OpenSeizureDetector/ESP8266_SD/osd_app_orig/adxl345/adxl345.h

/*
 * ADXL345 FreeRTOS Library Header File
 * Based on the Arduino ADXL345 library at 
 *    https://github.com/jarzebski/Arduino-ADXL345
 * (c) 2014 Korneliusz Jarzebski (www.jarzebski.pl)
 * Copyright Graham Jones, 2017.
 * 
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
 */

#include "espressif/esp_common.h"
#include "../i2c/i2c.h"






#ifndef ADXL345_h
#define ADXL345_h

#define ADXL345_ADDRESS              (0x1D)
#define ADXL345_ALT_ADDRESS          (0x53)
#define ADXL345_DEVID                (0xe5)

// ADXL Register locations
#define ADXL345_REG_DEVID            (0x00)
#define ADXL345_REG_THRESH_TAP       (0x1D) // 1
#define ADXL345_REG_OFSX             (0x1E)
#define ADXL345_REG_OFSY             (0x1F)
#define ADXL345_REG_OFSZ             (0x20)
#define ADXL345_REG_DUR              (0x21) // 2
#define ADXL345_REG_LATENT           (0x22) // 3
#define ADXL345_REG_WINDOW           (0x23) // 4
#define ADXL345_REG_THRESH_ACT       (0x24) // 5
#define ADXL345_REG_THRESH_INACT     (0x25) // 6
#define ADXL345_REG_TIME_INACT       (0x26) // 7
#define ADXL345_REG_ACT_INACT_CTL    (0x27)
#define ADXL345_REG_THRESH_FF        (0x28) // 8
#define ADXL345_REG_TIME_FF          (0x29) // 9
#define ADXL345_REG_TAP_AXES         (0x2A)
#define ADXL345_REG_ACT_TAP_STATUS   (0x2B)
#define ADXL345_REG_BW_RATE          (0x2C)
#define ADXL345_REG_POWER_CTL        (0x2D)
#define ADXL345_REG_INT_ENABLE       (0x2E)
#define ADXL345_REG_INT_MAP          (0x2F)
#define ADXL345_REG_INT_SOURCE       (0x30) // A
#define ADXL345_REG_DATA_FORMAT      (0x31)
#define ADXL345_REG_DATAX0           (0x32)
#define ADXL345_REG_DATAX1           (0x33)
#define ADXL345_REG_DATAY0           (0x34)
#define ADXL345_REG_DATAY1           (0x35)
#define ADXL345_REG_DATAZ0           (0x36)
#define ADXL345_REG_DATAZ1           (0x37)
#define ADXL345_REG_FIFO_CTL         (0x38)
#define ADXL345_REG_FIFO_STATUS      (0x39)

#define ADXL345_GRAVITY_SUN          273.95f
#define ADXL345_GRAVITY_EARTH        9.80665f
#define ADXL345_GRAVITY_MOON         1.622f
#define ADXL345_GRAVITY_MARS         3.69f
#define ADXL345_GRAVITY_NONE         1.00f

#ifndef VECTOR_STRUCT_H
#define VECTOR_STRUCT_H
typedef struct 
{
  float XAxis;
  float YAxis;
  float ZAxis;
} ADXL345_Vector;
#endif

#ifndef IVECTOR_STRUCT_H
#define IVECTOR_STRUCT_H
typedef struct 
{
  int16_t XAxis;
  int16_t YAxis;
  int16_t ZAxis;
} ADXL345_IVector;
#endif

typedef enum
{
    ADXL345_DATARATE_3200HZ    = 0b1111,
    ADXL345_DATARATE_1600HZ    = 0b1110,
    ADXL345_DATARATE_800HZ     = 0b1101,
    ADXL345_DATARATE_400HZ     = 0b1100,
    ADXL345_DATARATE_200HZ     = 0b1011,
    ADXL345_DATARATE_100HZ     = 0b1010,
    ADXL345_DATARATE_50HZ      = 0b1001,
    ADXL345_DATARATE_25HZ      = 0b1000,
    ADXL345_DATARATE_12_5HZ    = 0b0111,
    ADXL345_DATARATE_6_25HZ    = 0b0110,
    ADXL345_DATARATE_3_13HZ    = 0b0101,
    ADXL345_DATARATE_1_56HZ    = 0b0100,
    ADXL345_DATARATE_0_78HZ    = 0b0011,
    ADXL345_DATARATE_0_39HZ    = 0b0010,
    ADXL345_DATARATE_0_20HZ    = 0b0001,
    ADXL345_DATARATE_0_10HZ    = 0b0000
} ADXL345_dataRate_t;

typedef enum
{
    ADXL345_INT2 = 0b01,
    ADXL345_INT1 = 0b00
} ADXL345_int_t;

typedef enum
{
    ADXL345_DATA_READY         = 0x07,
    ADXL345_SINGLE_TAP         = 0x06,
    ADXL345_DOUBLE_TAP         = 0x05,
    ADXL345_ACTIVITY           = 0x04,
    ADXL345_INACTIVITY         = 0x03,
    ADXL345_FREE_FALL          = 0x02,
    ADXL345_WATERMARK          = 0x01,
    ADXL345_OVERRUN            = 0x00
} ADXL345_activity_t;

typedef enum
{
    ADXL345_RANGE_16G          = 0b11,
    ADXL345_RANGE_8G           = 0b10,
    ADXL345_RANGE_4G           = 0b01,
    ADXL345_RANGE_2G           = 0b00
} ADXL345_range_t;


typedef struct
{
    bool isOverrun;
    bool isWatermark;
    bool isFreeFall;
    bool isInactivity;
    bool isActivity;
    bool isActivityOnX;
    bool isActivityOnY;
    bool isActivityOnZ;
    bool isDoubleTap;
    bool isTap;
    bool isTapOnX;
    bool isTapOnY;
    bool isTapOnZ;
    bool isDataReady;
} ADXL345_Activites;

//bool ADXL345_begin(void);
void ADXL345_clearSettings(void);

ADXL345_IVector ADXL345_readRaw(void);
ADXL345_Vector ADXL345_readNormalize(float gravityFactor);
ADXL345_Vector ADXL345_readScaled(void);

ADXL345_Activites ADXL345_readActivites(void);

ADXL345_Vector ADXL345_lowPassFilter(ADXL345_Vector vector, float alpha);

void  ADXL345_setRange(ADXL345_range_t range);
ADXL345_range_t ADXL345_getRange(void);

void  ADXL345_setDataRate(ADXL345_dataRate_t dataRate);
ADXL345_dataRate_t ADXL345_getDataRate(void);

void ADXL345_setTapThreshold(float threshold);
float ADXL345_getTapThreshold(void);

void ADXL345_setTapDuration(float duration);
float ADXL345_getTapDuration(void);

void ADXL345_setDoubleTapLatency(float latency);
float ADXL345_getDoubleTapLatency(void);

void ADXL345_setDoubleTapWindow(float window);
float ADXL345_getDoubleTapWindow(void);

void ADXL345_setActivityThreshold(float threshold);
float ADXL345_getActivityThreshold(void);

void ADXL345_setInactivityThreshold(float threshold);
float ADXL345_getInactivityThreshold(void);

void ADXL345_setTimeInactivity(uint8_t time);
uint8_t ADXL345_getTimeInactivity(void);

void ADXL345_setFreeFallThreshold(float threshold);
float ADXL345_getFreeFallThreshold(void);

void ADXL345_setFreeFallDuration(float duration);
float ADXL345_getFreeFallDuration();

void ADXL345_setActivityX(bool state);
bool ADXL345_getActivityX(void);
void ADXL345_setActivityY(bool state);
bool ADXL345_getActivityY(void);
void ADXL345_setActivityZ(bool state);
bool ADXL345_getActivityZ(void);
void ADXL345_setActivityXYZ(bool state);

void ADXL345_setInactivityX(bool state);
bool ADXL345_getInactivityX(void);
void ADXL345_setInactivityY(bool state);
bool ADXL345_getInactivityY(void);
void ADXL345_setInactivityZ(bool state);
bool ADXL345_getInactivityZ(void);
void ADXL345_setInactivityXYZ(bool state);

void ADXL345_setTapDetectionX(bool state);
bool ADXL345_getTapDetectionX(void);
void ADXL345_setTapDetectionY(bool state);
bool ADXL345_getTapDetectionY(void);
void ADXL345_setTapDetectionZ(bool state);
bool ADXL345_getTapDetectionZ(void);
void ADXL345_setTapDetectionXYZ(bool state);

void ADXL345_useInterrupt(ADXL345_int_t interrupt);

void ADXL345_enableFifo(void);
uint8_t ADXL345_getFifoStatus(void);
uint8_t ADXL345_getFifoCtl(void);
uint8_t ADXL345_setFifoCtl(uint8_t ctlVal);

uint8_t ADXL345_writeRegister8(uint8_t reg, uint8_t value);
uint8_t ADXL345_readRegister8(uint8_t reg);
uint8_t ADXL345_fastRegister8(uint8_t reg);
int16_t ADXL345_readRegister16(uint8_t reg);
void ADXL345_writeRegisterBit(uint8_t reg, uint8_t pos, bool state);
bool ADXL345_readRegisterBit(uint8_t reg, uint8_t pos);





// Function prototypes
uint8_t ADXL345_init(int scl, int sca);


#endif
