OpenSeizureDetector/ESP8266_SD/osd_esp/user/comms.c

/*
 * OpenSeizureDetector - ESP8266 Version.
 *
 * ESP8266_SD - a simple accelerometer based seizure detector that runs on 
 * an ESP8266 system on chip, with ADXL345 accelerometer attached by i2c 
 * interface.
 *
 * See http://openseizuredetector.org for more information.
 *
 * Copyright Graham Jones, 2015, 2016, 2017
 *
 * This file is part of ESP8266_SD.
 *
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
 * You should have received a copy of the GNU General Public License
 * along with ESP8266_SD.  If not, see <http://www.gnu.org/licenses/>.
 */

#include <string.h>

#include <freertos/FreeRTOS.h>
#include <freertos/task.h>

#include "lwip/err.h"
#include "lwip/sockets.h"
#include "lwip/sys.h"
#include "lwip/netdb.h"
#include "lwip/dns.h"

#include "spiffs.h"
#include "esp_spiffs.h"


#include "private_ssid_config.h"

#include "osd_app.h"


#define WEB_IPADDR "192.168.43.77"
#define WEB_PORT 8080
#define WEB_URL "http://chainxor.org/"

#define BUF_SIZE 2000
#define REQ_SIZE 200

/**
 * int sendHttpRequest(serverIp,url,serverPort,reqType,contType,data,
 *                            response,maxlen)
 * sends a http GET request to server *serverIp with *url, port serverPort 
 * Request type reqType is GET, POST etc.
 * Content type is application/json etc.
 * Character string data is included in the request body.
 * and put the response in *response
 * which should have maxLen bytes reserved for it.
 * returns the number of bytes read.
 */
int sendHttpRequest(char *serverIp, char *url, int serverPort, char *reqType,
		    char *contType, char *data,
		   char *response, int maxLen) {
  struct sockaddr_in ipaddr;
  static char req[REQ_SIZE];
  int ret;
  int s;  // socket id.
  
  if (debug) APP_LOG(APP_LOG_LEVEL_DEBUG,"sendHttpRequest(%s)", url);
  
  // set up server address
  memset(&ipaddr,0,sizeof(ipaddr));
  ipaddr.sin_len = sizeof(ipaddr);
  ipaddr.sin_family = AF_INET;
  ipaddr.sin_port = PP_HTONS(serverPort);
  ipaddr.sin_addr.s_addr = inet_addr(serverIp);
  printf("processed IP Address = %s\n", ipaddr_ntoa((ip_addr_t*)&(ipaddr.sin_addr.s_addr)));

  // create socket
  s = lwip_socket(AF_INET, SOCK_STREAM, 0);
  if(s < 0) {
    printf("sendHttpRequest()... Failed to allocate socket.");
    return -1;
  } else
      if (debug) APP_LOG(APP_LOG_LEVEL_DEBUG,
			 "sendHttpRequest() - allocated socket ok");

  // connect
  ret = lwip_connect(s, (struct sockaddr*)&ipaddr, sizeof(ipaddr));
  if(ret!=0) {
    close(s);
    printf("sendHttpRequest() - **** FAILED TO CONNECT ***\n");
    return -1 ;
  } else {
    if (debug) APP_LOG(APP_LOG_LEVEL_DEBUG,
		       "sendHttpRequest() - connected ok");
  }

  snprintf(req,REQ_SIZE,
    "%s %s HTTP/1.0\r\n"
    "User-Agent: esp-open-rtos/0.1 esp8266\r\n"
	   "Content-Type: %s\r\n"
	   "Content-Length:%d\r\n"
	   "\r\n"
	   "%s\r\n"
	   ,reqType,url,contType,strlen(data),data);
  if (debug) APP_LOG(APP_LOG_LEVEL_DEBUG,
		     "sendHttpRequest() - req=%s",req);
  if (lwip_write(s, req, strlen(req)) < 0) {
    printf("sendHttpRequest()... socket send failed");
  } else {
    if (debug) APP_LOG(APP_LOG_LEVEL_DEBUG,
		       "sendHttpRequest() - send ok");
  }

  // zero the response buffer, then read the response.
  bzero(response, maxLen);
  ret = lwip_read(s,response,maxLen);
  if (debug) APP_LOG(APP_LOG_LEVEL_DEBUG,
		     "sendHttpRequest() - Read data from socket - ret=%d.  response=%s.",ret,response);
  
  lwip_close(s);
  if (debug) APP_LOG(APP_LOG_LEVEL_DEBUG,
  		     "sendHttpRequest() - Socket closed - Returning %d",ret);
  return ret;
}

/** 
 * int sendGetRequest(serverIp,url,serverPort,response,maxlen)
 * sends a http GET request to server *serverIp with *url, port serverPort 
 * and put the response in *response
 * which should have maxLen bytes reserved for it.
 * returns the number of bytes read.
 */
int sendGetRequest(char *serverIp, char *url, int serverPort,
		   char *response, int maxLen) {
  int r;
  if (debug) APP_LOG(APP_LOG_LEVEL_DEBUG,"sendGetRequest(%s)", url);
  r = sendHttpRequest(serverIp,url,serverPort,
		      "GET","application/json","",response,maxLen);
  return r;
}

/** 
 * int sendPostRequest(serverIp,url,serverPort,data,response,maxlen)
 * sends a http GET request to server *serverIp with *url, port serverPort 
 * including *data in the header, and put the response in *response
 * which should have maxLen bytes reserved for it.
 * returns the number of bytes read.
 */
int sendPostRequest(char *serverIp, char *url, int serverPort, char *data,
		   char *response, int maxLen) {
  int r;
  if (debug) APP_LOG(APP_LOG_LEVEL_DEBUG,"sendPostRequest(%s)", url);
  r = sendHttpRequest(serverIp,url,serverPort,
		      "POST","application/json",data,response,maxLen);
  //if (debug) APP_LOG(APP_LOG_LEVEL_DEBUG,"sendPostRequest complete");
  return r;
}



/***************************************************
 * Send some Seizure Detector Data to the phone app.
 */

void sendSdData() {
  static char buf[BUF_SIZE];
  int ret;
  if (debug) APP_LOG(APP_LOG_LEVEL_DEBUG,"sendSdData()");
  ret = sendPostRequest(WEB_IPADDR,"/data",WEB_PORT,
			"{\"data\":{\"nsamp\":500,\"roiPower\":200,\"specPower\":30}}",
			buf,BUF_SIZE);
  if (debug) APP_LOG(APP_LOG_LEVEL_DEBUG,"sendSdData() - response=%d - %s",
		     ret,buf);

}
/*
  DictionaryIterator *iter;
  if (debug) APP_LOG(APP_LOG_LEVEL_DEBUG,"sendSdData()");
  app_message_outbox_begin(&iter);
  dict_write_uint8(iter,KEY_DATA_TYPE,(uint8_t)DATA_TYPE_RESULTS);
  dict_write_uint8(iter,KEY_ALARMSTATE,(uint8_t)alarmState);
  dict_write_uint32(iter,KEY_MAXVAL,(uint32_t)maxVal);
  dict_write_uint32(iter,KEY_MAXFREQ,(uint32_t)maxFreq);
  dict_write_uint32(iter,KEY_SPECPOWER,(uint32_t)specPower);
  dict_write_uint32(iter,KEY_ROIPOWER,(uint32_t)roiPower);
  dict_write_uint32(iter,KEY_ALARM_ROI,(uint32_t)alarmRoi);
  // Send simplified spectrum - just 10 integers so it fits in a message.
  dict_write_data(iter,KEY_SPEC_DATA,(uint8_t*)(&simpleSpec[0]),
		  10*sizeof(simpleSpec[0]));
  app_message_outbox_send();
  if (debug) APP_LOG(APP_LOG_LEVEL_DEBUG,"sent Results");
}
*/




/*************************************************************
 * Communications with Phone
 *************************************************************/
/*void inbox_received_callback(DictionaryIterator *iterator, void *context) {
  APP_LOG(APP_LOG_LEVEL_INFO, "Message received!");
  // Get the first pair
  Tuple *t = dict_read_first(iterator);

  int settingsChanged = 0;
  
  // Process all pairs present
  while(t != NULL) {
    // Process this pair's key
    APP_LOG(APP_LOG_LEVEL_INFO,"Key=%d",(int) t->key);
    switch (t->key) {
    case KEY_SETTINGS:
      APP_LOG(APP_LOG_LEVEL_INFO, "***********Phone Requesting Settings");
      sendSettings();
      break;
    case KEY_DATA_TYPE:
      APP_LOG(APP_LOG_LEVEL_INFO, "***********Phone Requesting Data");
      sendSdData();
      break;
    case KEY_SET_SETTINGS:
      APP_LOG(APP_LOG_LEVEL_INFO, "***********Phone Setting Settings");
      // We don't actually do anything here - the following sections
      // process the data and update the settings.
      break;
    case KEY_DEBUG:
      APP_LOG(APP_LOG_LEVEL_INFO,"Phone Setting DEBUG to %d",
	      debug = (int)t->value->int16);
      break;
    case KEY_DISPLAY_SPECTRUM:
      APP_LOG(APP_LOG_LEVEL_INFO,"Phone Setting DISPLAY_SPECTRUM to %d",
	      displaySpectrum = (int)t->value->int16);
      break;
    case KEY_SAMPLE_PERIOD:
      APP_LOG(APP_LOG_LEVEL_INFO,"Phone Setting SAMPLE_PERIOD to %d",
	      samplePeriod = (int)t->value->int16);
      settingsChanged = 1;
      break;
    case KEY_SAMPLE_FREQ:
      APP_LOG(APP_LOG_LEVEL_INFO,"Phone Setting SAMPLE_FREQ to %d",
	      sampleFreq = (int)t->value->int16);
      settingsChanged = 1;
      break;
    case KEY_FREQ_CUTOFF:
      APP_LOG(APP_LOG_LEVEL_INFO,"Phone Setting FREQ_CUTOFF to %d",
	      freqCutoff = (int)t->value->int16);
      settingsChanged = 1;
      break;
    case KEY_DATA_UPDATE_PERIOD:
      APP_LOG(APP_LOG_LEVEL_INFO,"Phone Setting DATA_UPDATE_PERIOD to %d",
	      dataUpdatePeriod = (int)t->value->int16);
      break;
    case KEY_SD_MODE:
      APP_LOG(APP_LOG_LEVEL_INFO,"Phone Setting SD_MODE to %d",
	      sdMode = (int)t->value->int16);
      break;
    case KEY_ALARM_FREQ_MIN:
      APP_LOG(APP_LOG_LEVEL_INFO,"Phone Setting ALARM_FREQ_MIN to %d",
	      alarmFreqMin = (int)t->value->int16);
      break;
    case KEY_ALARM_FREQ_MAX:
      APP_LOG(APP_LOG_LEVEL_INFO,"Phone Setting ALARM_FREQ_MAX to %d",
	      alarmFreqMax = (int)t->value->int16);
      break;
    case KEY_WARN_TIME:
      APP_LOG(APP_LOG_LEVEL_INFO,"Phone Setting WARN_TIME to %d",
	      warnTime = (int)t->value->int16);
      break;
    case KEY_ALARM_TIME:
      APP_LOG(APP_LOG_LEVEL_INFO,"Phone Setting ALARM_TIME to %d",
	      alarmTime = (int)t->value->int16);
      break;
    case KEY_ALARM_THRESH:
      APP_LOG(APP_LOG_LEVEL_INFO,"Phone Setting ALARM_THRESH to %d",
	      alarmThresh = (int)t->value->int16);
      break;
    case KEY_ALARM_RATIO_THRESH:
      APP_LOG(APP_LOG_LEVEL_INFO,"Phone Setting ALARM_RATIO_THRESH to %d",
	      alarmRatioThresh = (int)t->value->int16);
      break;
    case KEY_FALL_ACTIVE:
      APP_LOG(APP_LOG_LEVEL_INFO,"Phone Setting FALL_ACTIVE to %d",
	      fallActive = (int)t->value->int16);
      break;
    case KEY_FALL_THRESH_MIN:
      APP_LOG(APP_LOG_LEVEL_INFO,"Phone Setting FALL_THRESH_MIN to %d",
	      fallThreshMin = (int)t->value->int16);
      break;
    case KEY_FALL_THRESH_MAX:
      APP_LOG(APP_LOG_LEVEL_INFO,"Phone Setting FALL_THRESH_MAX to %d",
	      fallThreshMax = (int)t->value->int16);
      break;
    case KEY_FALL_WINDOW:
      APP_LOG(APP_LOG_LEVEL_INFO,"Phone Setting FALL_WINDOW to %d",
	      fallWindow = (int)t->value->int16);
      break;
    case KEY_MUTE_PERIOD:
      APP_LOG(APP_LOG_LEVEL_INFO,"Phone Setting MUTE_PERIOD to %d",
	      mutePeriod = (int)t->value->int16);
      break;
    case KEY_MAN_ALARM_PERIOD:
      APP_LOG(APP_LOG_LEVEL_INFO,"Phone Setting MAN_ALARM_PERIOD to %d",
	      manAlarmPeriod = (int)t->value->int16);
      break;
    }
    // Get next pair, if any
    t = dict_read_next(iterator);
  }
  if (settingsChanged) {
    APP_LOG(APP_LOG_LEVEL_DEBUG,"Accelerometer Settings Changed - resetting");
    analysis_init();
  }
}
*/

/*
void inbox_dropped_callback(AppMessageResult reason, void *context) {
  APP_LOG(APP_LOG_LEVEL_ERROR, "Message dropped!");
}
*/

/*
void outbox_failed_callback(DictionaryIterator *iterator, AppMessageResult reason, void *context) {
  APP_LOG(APP_LOG_LEVEL_ERROR, "Outbox send failed!");
}

void outbox_sent_callback(DictionaryIterator *iterator, void *context) {
  if (debug) APP_LOG(APP_LOG_LEVEL_INFO, "Outbox send success!");
}
*/

/*******************************************************
 * Send raw accelerometer data to the phone
 */
void sendRawData(ADXL345_IVector *data, uint32_t num_samples) {
  if (debug) APP_LOG(APP_LOG_LEVEL_DEBUG,"sendRawData() - num_samples=%d",num_samples);
}

/*void sendRawData(AccelData *data, uint32_t num_samples) {
  DictionaryIterator *iter;
  int32_t accData[25];  // 25 samples.
  for (uint8_t i=0;i<num_samples;i++) {
    accData[i] =
        data[i].x*data[i].x
      + data[i].y*data[i].y
      + data[i].z*data[i].z;
    //accData[3*i] = data[i].x;
    //accData[3*i+1] = data[i].y;
    //accData[3*i+2] = data[i].z;
  }
  if (debug) APP_LOG(APP_LOG_LEVEL_DEBUG,"sendRawData() - num_samples=%ld",num_samples);
  app_message_outbox_begin(&iter);
  dict_write_uint8(iter,KEY_DATA_TYPE,(uint8_t)DATA_TYPE_RAW);
  dict_write_uint32(iter,KEY_NUM_RAW_DATA,(uint32_t)num_samples);
  dict_write_data(iter,KEY_RAW_DATA,(uint8_t*)(accData),
		  num_samples*sizeof(accData[0]));
  app_message_outbox_send();
  if (debug) APP_LOG(APP_LOG_LEVEL_DEBUG,"sent Results");
}
*/

/***************************************************
 * Send Seizure Detector Settings to the Phone
 */
/*
void sendSettings() {
  DictionaryIterator *iter;
  APP_LOG(APP_LOG_LEVEL_INFO, "sendSettings()");
  app_message_outbox_begin(&iter);
  // Tell the phone this is settings data
  dict_write_uint8(iter,KEY_DATA_TYPE,(uint8_t)DATA_TYPE_SETTINGS);
  dict_write_uint8(iter,KEY_SETTINGS,(uint8_t)1);
  // then the actual settings
  dict_write_uint32(iter,KEY_DEBUG,(uint32_t)debug);
  dict_write_uint32(iter,KEY_DISPLAY_SPECTRUM,(uint32_t)displaySpectrum);
  // first the app version number
  dict_write_uint8(iter,KEY_VERSION_MAJOR,
		   (uint8_t)__pbl_app_info.process_version.major);
  dict_write_uint8(iter,KEY_VERSION_MINOR,
		   (uint8_t)__pbl_app_info.process_version.minor);
  // then the settings
  dict_write_uint32(iter,KEY_SAMPLE_PERIOD,(uint32_t)samplePeriod);
  dict_write_uint32(iter,KEY_SAMPLE_FREQ,(uint32_t)sampleFreq);
  dict_write_uint32(iter,KEY_FREQ_CUTOFF,(uint32_t)freqCutoff);
  dict_write_uint32(iter,KEY_DATA_UPDATE_PERIOD,(uint32_t)dataUpdatePeriod);
  dict_write_uint32(iter,KEY_SD_MODE,(uint32_t)sdMode);
  dict_write_uint32(iter,KEY_ALARM_FREQ_MIN,(uint32_t)alarmFreqMin);
  dict_write_uint32(iter,KEY_ALARM_FREQ_MAX,(uint32_t)alarmFreqMax);
  dict_write_uint32(iter,KEY_NMIN,(uint32_t)nMin);
  dict_write_uint32(iter,KEY_NMAX,(uint32_t)nMax);
  dict_write_uint32(iter,KEY_WARN_TIME,(uint32_t)warnTime);
  dict_write_uint32(iter,KEY_ALARM_TIME,(uint32_t)alarmTime);
  dict_write_uint32(iter,KEY_ALARM_THRESH,(uint32_t)alarmThresh);
  dict_write_uint32(iter,KEY_ALARM_RATIO_THRESH,(uint32_t)alarmRatioThresh);
  BatteryChargeState charge_state = battery_state_service_peek();
  dict_write_uint8(iter,KEY_BATTERY_PC,(uint8_t)charge_state.charge_percent);
  dict_write_uint32(iter,KEY_FALL_ACTIVE,(uint32_t)fallActive);
  dict_write_uint32(iter,KEY_FALL_THRESH_MIN,(uint32_t)fallThreshMin);
  dict_write_uint32(iter,KEY_FALL_THRESH_MAX,(uint32_t)fallThreshMax);
  dict_write_uint32(iter,KEY_FALL_WINDOW,(uint32_t)fallWindow);
  dict_write_uint32(iter,KEY_MUTE_PERIOD,(uint32_t)mutePeriod);
  dict_write_uint32(iter,KEY_MAN_ALARM_PERIOD,(uint32_t)manAlarmPeriod);

  app_message_outbox_send();

}
*/

void comms_init() {
  APP_LOG(APP_LOG_LEVEL_INFO, "comms_init()");

  struct station_config config = {
    .ssid = WIFI_SSID,
    .password = WIFI_PASS,
  };
  
  /* required to call wifi_set_opmode before station_set_config */
  wifi_set_opmode(STATION_MODE);
  wifi_station_set_config(&config);
  wifi_station_connect();

  
  /*
  // Register comms callbacks
  app_message_register_inbox_received(inbox_received_callback);
  APP_LOG(APP_LOG_LEVEL_INFO, "comms_init() - registered inbox_received_callback.");
  app_message_register_inbox_dropped(inbox_dropped_callback);
  APP_LOG(APP_LOG_LEVEL_INFO, "comms_init() - registered inbox_dropped_callback.");
  app_message_register_outbox_failed(outbox_failed_callback);
  APP_LOG(APP_LOG_LEVEL_INFO, "comms_init() - registered outbox_failed_callback.");
  app_message_register_outbox_sent(outbox_sent_callback);
  APP_LOG(APP_LOG_LEVEL_INFO, "comms_init() - registered outbox_failed_callback.");
  // Open AppMessage
  //int retVal = app_message_open(app_message_inbox_size_maximum(), 
  //		   app_message_outbox_size_maximum());
  int retVal = app_message_open(INBOX_SIZE, 
  				OUTBOX_SIZE);

  if (retVal == APP_MSG_OK) 
    APP_LOG(APP_LOG_LEVEL_INFO, "comms_init() - app_message_open() Success - retVal=%d, inbox_size=%d, outbox_size=%d",retVal,
	  INBOX_SIZE,
	  OUTBOX_SIZE);
  else if (retVal == APP_MSG_OUT_OF_MEMORY)
    APP_LOG(APP_LOG_LEVEL_ERROR, "comms_init() - app_message_open() **** OUT_OF_MEMORY **** - retVal=%d, max_inbox_size=%d, max_outbox_size=%d",retVal,
	  INBOX_SIZE,
	  OUTBOX_SIZE);
  else
    APP_LOG(APP_LOG_LEVEL_ERROR, "comms_init() - app_message_open() - retVal=%d, max_inbox_size=%d, max_outbox_size=%d",retVal,
	  INBOX_SIZE,
	  OUTBOX_SIZE);

  */


}


/* 
 *  waits for a message from the queue.  When received, sends
 *  the SD Data to the server.
*/
void commsTask(void *pvParameters)
{
  xQueueHandle *commsQueue = (xQueueHandle *)pvParameters;

  while(1) {
    uint32_t data_ts;
    xQueueReceive(*commsQueue, &data_ts, portMAX_DELAY);
    APP_LOG(APP_LOG_LEVEL_INFO, "commsTask()");
    sendSdData();
  }
}
