OpenSeizureDetector/ESP8266_SD/osd_esp/driver/i2c.c

/* 
 * The MIT License (MIT)
 * 
 * Copyright (c) 2015 Johan Kanflo (github.com/kanflo)
 *               2017 Graham Jones (github.com/jones139)
 * 
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
 * THE SOFTWARE IS PROVIDED "AS IS", WITHOUT WARRANTY OF ANY KIND, EXPRESS OR
 * IMPLIED, INCLUDING BUT NOT LIMITED TO THE WARRANTIES OF MERCHANTABILITY,
 * FITNESS FOR A PARTICULAR PURPOSE AND NONINFRINGEMENT. IN NO EVENT SHALL THE
 * AUTHORS OR COPYRIGHT HOLDERS BE LIABLE FOR ANY CLAIM, DAMAGES OR OTHER
 * LIABILITY, WHETHER IN AN ACTION OF CONTRACT, TORT OR OTHERWISE, ARISING FROM,
 * OUT OF OR IN CONNECTION WITH THE SOFTWARE OR THE USE OR OTHER DEALINGS IN
 * THE SOFTWARE.
 */

/**
 * Note:  This is the esp-open-rtos sdk i2c driver modified to work with the
 *        Espressif RTOS sdk rather than esp-open-rtos.
 *        I did this because esp-open-rtos does not support low power sleep
 *        functions which I need, and it looks too hard to reverse engineer
 *        it.
 *        Graham Jones, August 2017.
 */

#include <espressif/esp_common.h>
#include <espressif/esp8266/esp8266.h>
//#include <espressif/esp_misc.h> // sdk_os_delay_us
//#include <espressif/esp_system.h>
#include "i2c.h"
#include "gpio.h"

#define I2C_DEBUG true

#ifdef I2C_DEBUG
#define debug(fmt, ...) printf("%s: " fmt "\n", "I2C", ## __VA_ARGS__)
#else
#define debug(fmt, ...)
#endif

#define CLK_STRETCH  (10)

static bool started;
static bool flag;
static bool force;
static uint8_t freq ;
static uint8_t g_scl_pin;
static uint8_t g_sda_pin;

//Return the Multiplexer value associated with gpio Pin number gpioPin
int gpioPin2Mux(int gpioPin) {
  switch (gpioPin) {
  case 0:
    return GPIO_PIN_REG_0;
  case 1:
    return GPIO_PIN_REG_1;
  case 2:
    return GPIO_PIN_REG_2;
  case 3:
    return GPIO_PIN_REG_3;
  case 4:
    return GPIO_PIN_REG_4;
  case 5:
    return GPIO_PIN_REG_5;
  case 6:
    return GPIO_PIN_REG_6;
  case 7:
    return GPIO_PIN_REG_7;
  case 8:
    return GPIO_PIN_REG_8;
  case 9:
    return GPIO_PIN_REG_9;
  case 10:
    return GPIO_PIN_REG_10;
  case 11:
    return GPIO_PIN_REG_11;
  case 12:
    return GPIO_PIN_REG_12;
  case 13:
    return GPIO_PIN_REG_13;
  case 14:
    return GPIO_PIN_REG_14;
  case 15:
    return GPIO_PIN_REG_15;
  default:
    return -1;
  }
  
}

//Return the gpio func value associated with gpio Pin number gpioPin
int gpioPin2Func(int gpioPin) {
  switch (gpioPin) {
    case 0:
      return FUNC_GPIO0;
    case 1:
      return FUNC_GPIO1;
    case 2:
      return FUNC_GPIO2;
    case 3:
      return FUNC_GPIO3;
    case 4:
      return FUNC_GPIO4;
    case 5:
      return FUNC_GPIO5;
    case 6:
      return FUNC_GPIO6;
    case 7:
      return FUNC_GPIO7;
    case 8:
      return FUNC_GPIO8;
    case 9:
      return FUNC_GPIO9;
    case 10:
      return FUNC_GPIO10;
    default:
      return -1;
    }
}

#define I2C_GPIO_SET(pin)  \
    gpio_output_set(1<<pin,0,1<<pin,0)

#define I2C_GPIO_CLR(pin) \
    gpio_output_set(0,1<<pin,1<<pin,0)

#define gpio_write(pin,val) \
    if(val) I2C_GPIO_SET(pin);\
    else I2C_GPIO_CLR(pin)

// return value of GPIO pin pin.
uint8 gpio_read(int pin) {
  uint8 val; 
  ETS_INTR_LOCK(); 
  val = GPIO_INPUT_GET(GPIO_ID_PIN(pin));
  ETS_INTR_UNLOCK(); 
  return val;
}

inline bool i2c_status(void)
{
    return started;
}

void i2c_init(uint8_t scl_pin, uint8_t sda_pin)
{
  printf("i2c_init - GJ Version\n");
    started = false;
    flag = false ;
    g_scl_pin = scl_pin;
    g_sda_pin = sda_pin;

    int sda_mux, scl_mux;
    int sda_func, scl_func;

    PIN_FUNC_SELECT(gpioPin2Mux(g_sda_pin), gpioPin2Func(g_sda_pin));
    PIN_FUNC_SELECT(gpioPin2Mux(g_scl_pin), gpioPin2Func(g_scl_pin));

    GPIO_REG_WRITE(
		   GPIO_PIN_ADDR(GPIO_ID_PIN(g_sda_pin)),
		   GPIO_REG_READ(GPIO_PIN_ADDR(GPIO_ID_PIN(g_sda_pin)))
		   | GPIO_PIN_PAD_DRIVER_SET(GPIO_PAD_DRIVER_ENABLE)
		   ); //open drain
    GPIO_REG_WRITE(
		   GPIO_ENABLE_ADDRESS,
		   GPIO_REG_READ(GPIO_ENABLE_ADDRESS) | (1 << g_sda_pin)
		   );
    GPIO_REG_WRITE(GPIO_PIN_ADDR(GPIO_ID_PIN(g_scl_pin)),
		   GPIO_REG_READ(GPIO_PIN_ADDR(GPIO_ID_PIN(g_scl_pin)))
		   | GPIO_PIN_PAD_DRIVER_SET(GPIO_PAD_DRIVER_ENABLE)
		   ); //open drain;
    GPIO_REG_WRITE(GPIO_ENABLE_ADDRESS,
		   GPIO_REG_READ(GPIO_ENABLE_ADDRESS) | (1 << g_scl_pin)
		   );

    // I2C bus idle state.
    gpio_write(g_scl_pin, 1);
    gpio_write(g_sda_pin, 1);

    ETS_GPIO_INTR_ENABLE() ;

    // Prevent user, if frequency is high
    //if (system_get_cpu_freq() == SYS_CPU_80MHZ)
    //    if (I2C_CUSTOM_DELAY_80MHZ == 1)
    //        debug("Max frequency is 320Khz at 80MHz");
}

static inline void i2c_delay(void)
{
    uint32_t delay;
    if (freq == SYS_CPU_160MHZ)
    {
        __asm volatile (
            "movi %0, %1" "\n"
            "1: addi %0, %0, -1" "\n"
            "bnez %0, 1b" "\n"
        : "=a" (delay) : "i" (I2C_CUSTOM_DELAY_160MHZ));
    }
    else
    {
        __asm volatile (
            "movi %0, %1" "\n"
            "1: addi %0, %0, -1" "\n"
            "bnez %0, 1b" "\n"
        : "=a" (delay) : "i" (I2C_CUSTOM_DELAY_80MHZ));
    }
}

// Set SCL as input, allowing it to float high, and return current
// level of line, 0 or 1
static inline bool read_scl(void)
{
    gpio_write(g_scl_pin, 1);
    return gpio_read(g_scl_pin); // Clock high, valid ACK
}

// Set SDA as input, allowing it to float high, and return current
// level of line, 0 or 1
static inline bool read_sda(void)
{
    gpio_write(g_sda_pin, 1);
    // TODO: Without this delay we get arbitration lost in i2c_stop
    i2c_delay();
    return gpio_read(g_sda_pin); // Clock high, valid ACK
}

// Actively drive SCL signal low
static inline void clear_scl(void)
{
    gpio_write(g_scl_pin, 0);
}

// Actively drive SDA signal low
static inline void clear_sda(void)
{
    gpio_write(g_sda_pin, 0);
}

// Output start condition
void i2c_start(void)
{
    uint32_t clk_stretch = CLK_STRETCH;
    freq = system_get_cpu_freq();
    if (started) { // if started, do a restart cond
        // Set SDA to 1
        (void) read_sda();
        i2c_delay();
        while (read_scl() == 0 && clk_stretch--) ;
        // Repeated start setup time, minimum 4.7us
        i2c_delay();
    }
    started = true;
    if (read_sda() == 0) {
        debug("arbitration lost in i2c_start");
    }
    // SCL is high, set SDA from 1 to 0.
    clear_sda();
    i2c_delay();
    clear_scl();
}

// Output stop condition
bool i2c_stop(void)
{
    uint32_t clk_stretch = CLK_STRETCH;
    // Set SDA to 0
    clear_sda();
    i2c_delay();
    // Clock stretching
    while (read_scl() == 0 && clk_stretch--) ;
    // Stop bit setup time, minimum 4us
    i2c_delay();
    // SCL is high, set SDA from 0 to 1
    if (read_sda() == 0) {
        debug("arbitration lost in i2c_stop");
    }
    i2c_delay();
    if (!started) {
        debug("link was break!");
        return false ; //If bus was stop in other way, the current transmission Failed
    }
    started = false;
    return true;
}

// Write a bit to I2C bus
static void i2c_write_bit(bool bit)
{
    uint32_t clk_stretch = CLK_STRETCH;
    if (bit) {
        (void) read_sda();
    } else {
        clear_sda();
    }
    i2c_delay();
    // Clock stretching
    while (read_scl() == 0 && clk_stretch--) ;
    // SCL is high, now data is valid
    // If SDA is high, check that nobody else is driving SDA
    if (bit && read_sda() == 0) {
        debug("arbitration lost in i2c_write_bit");
    }
    i2c_delay();
    clear_scl();
}

// Read a bit from I2C bus
static bool i2c_read_bit(void)
{
    uint32_t clk_stretch = CLK_STRETCH;
    bool bit;
    // Let the slave drive data
    (void) read_sda();
    i2c_delay();
    // Clock stretching
    while (read_scl() == 0 && clk_stretch--) ;
    // SCL is high, now data is valid
    bit = read_sda();
    i2c_delay();
    clear_scl();
    return bit;
}

bool i2c_write(uint8_t byte)
{
    bool nack;
    uint8_t bit;
    for (bit = 0; bit < 8; bit++) {
        i2c_write_bit((byte & 0x80) != 0);
        byte <<= 1;
    }
    nack = i2c_read_bit();
    return !nack;
}

uint8_t i2c_read(bool ack)
{
    uint8_t byte = 0;
    uint8_t bit;
    for (bit = 0; bit < 8; bit++) {
        byte = (byte << 1) | i2c_read_bit();
    }
    i2c_write_bit(ack);
    return byte;
}

void i2c_force_bus(bool state)
{
    force = state ;
}

static int i2c_bus_test()
{
    taskENTER_CRITICAL(); // To prevent task swaping after checking flag and before set it!
    bool status = flag ; // get current status
    if(force)
    {
        flag = true ; // force bus on
        taskEXIT_CRITICAL();
        if(status)
           i2c_stop(); //Bus was busy, stop it.
    }
    else
    {
        if (status)
        {
            taskEXIT_CRITICAL();
            debug("busy");
            taskYIELD(); // If bus busy, change task to try finish last com.
            return -EBUSY ;  // If bus busy, inform user
        }
        else
        {
            flag = true ; // Set Bus busy
            taskEXIT_CRITICAL();
        }
    }
    return 0 ;
}

int i2c_slave_write(uint8_t slave_addr, const uint8_t *data, const uint8_t *buf, uint32_t len)
{
    if(i2c_bus_test())
        return -EBUSY ;
    i2c_start();
    if (!i2c_write(slave_addr << 1))
        goto error;
    if(data != NULL)
        if (!i2c_write(*data))
            goto error;
    while (len--) {
        if (!i2c_write(*buf++))
            goto error;
    }
    if (!i2c_stop())
        goto error;
    flag = false ; // Bus free
    return 0;

    error:
    debug("Write Error");
    i2c_stop();
    flag = false ; // Bus free
    return -EIO;
}

int i2c_slave_read(uint8_t slave_addr, const uint8_t *data, uint8_t *buf, uint32_t len)
{
    if(i2c_bus_test())
        return -EBUSY ;
    if(data != NULL) {
        i2c_start();
        if (!i2c_write(slave_addr << 1))
            goto error;
        if (!i2c_write(*data))
            goto error;
        if (!i2c_stop())
            goto error;
    }
    i2c_start();
    if (!i2c_write(slave_addr << 1 | 1)) // Slave address + read
        goto error;
    while(len) {
        *buf = i2c_read(len == 1);
        buf++;
        len--;
    }
    if (!i2c_stop())
        goto error;
    flag = false ; // Bus free
    return 0;

    error:
    debug("Read Error");
    i2c_stop();
    flag = false ; // Bus free
    return -EIO;
}
